Yiqian7a/AI-Cat-Feeder/README.assets/image-20230812141946083.png

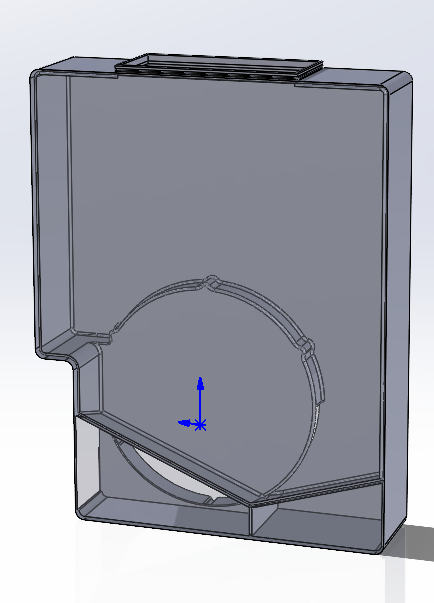
README.assets/image-20230812141946083.png
