Yiqian7a/AI-Cat-Feeder/README.assets/image-20230812142354347.png

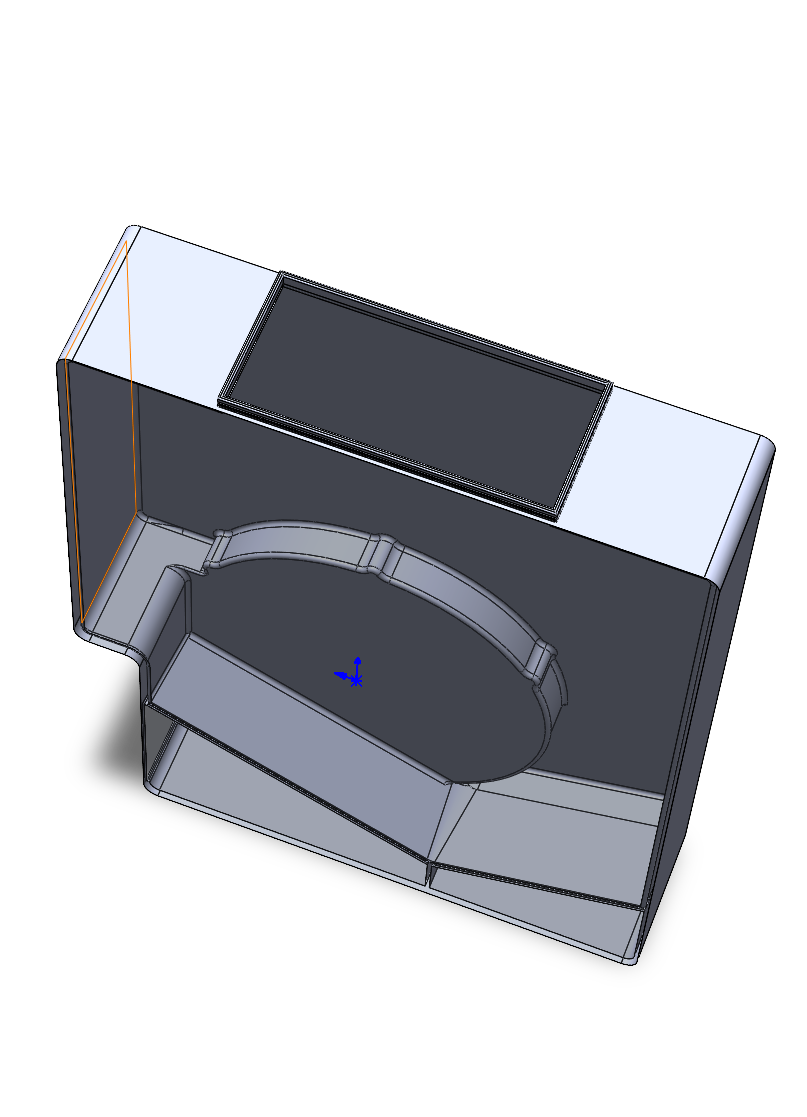
README.assets/image-20230812142354347.png
